seuros/epdiy-esp-idf-6/doc/source/img/board_p2.jpg

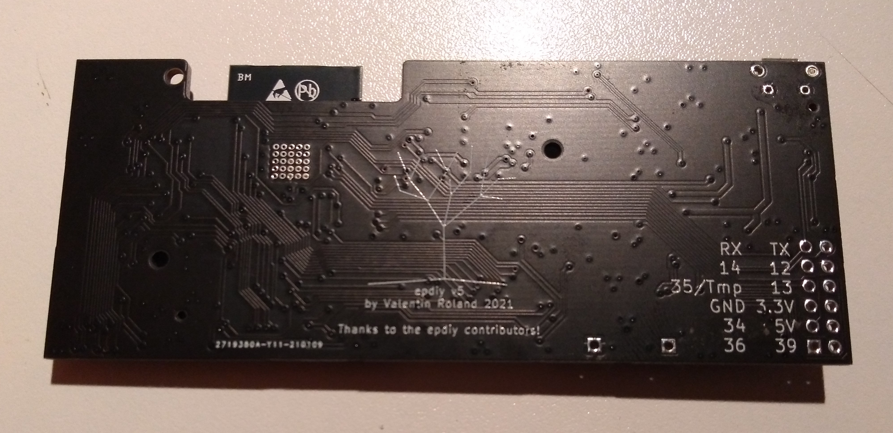
doc/source/img/board_p2.jpg
