seuros/epdiy-esp-idf-6/doc/source/img/ed060sc4.jpg

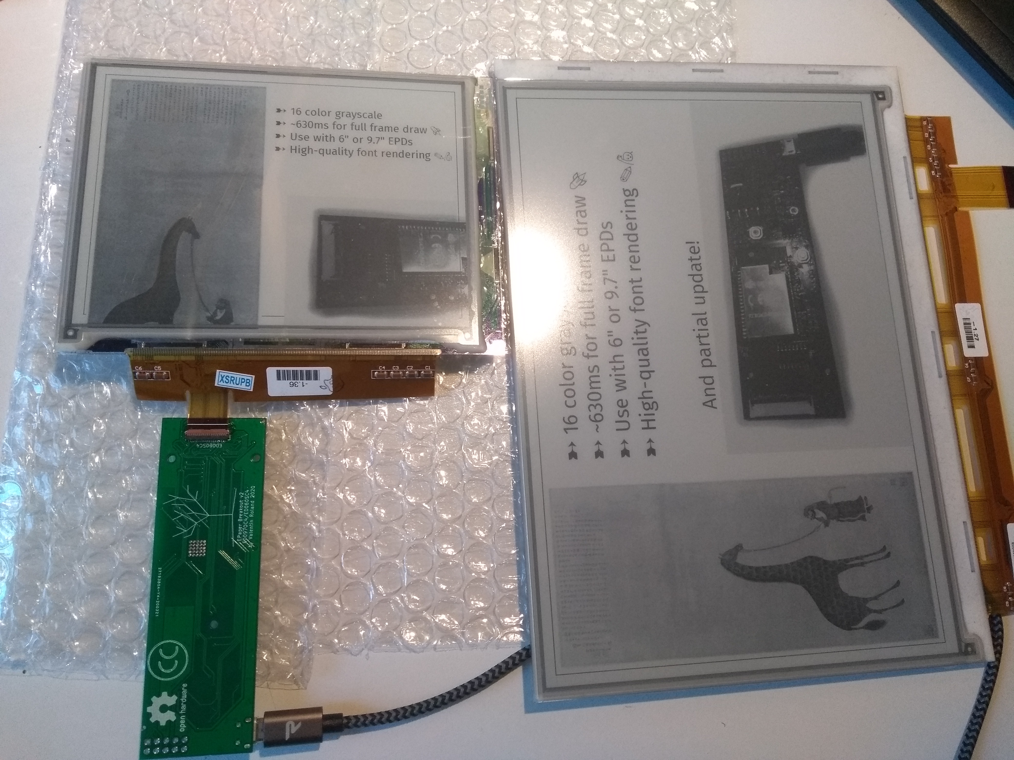
doc/source/img/ed060sc4.jpg
