seuros/epdiy-esp-idf-6/examples/demo/files/beach.jpg

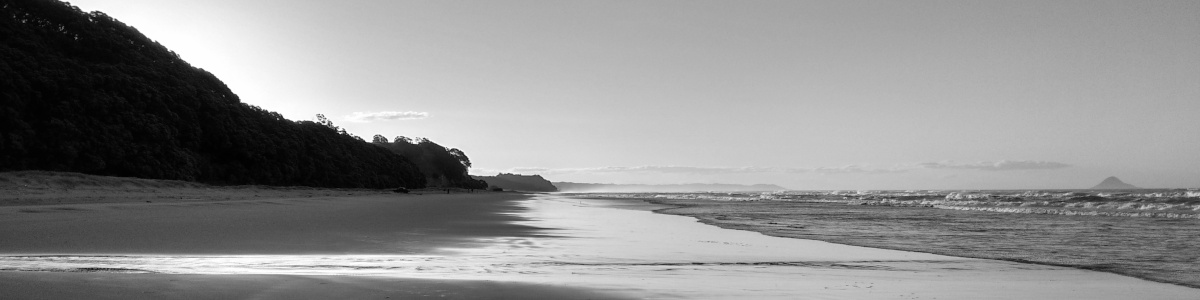
examples/demo/files/beach.jpg
