seuros/epdiy-esp-idf-6/examples/demo/files/board.jpg

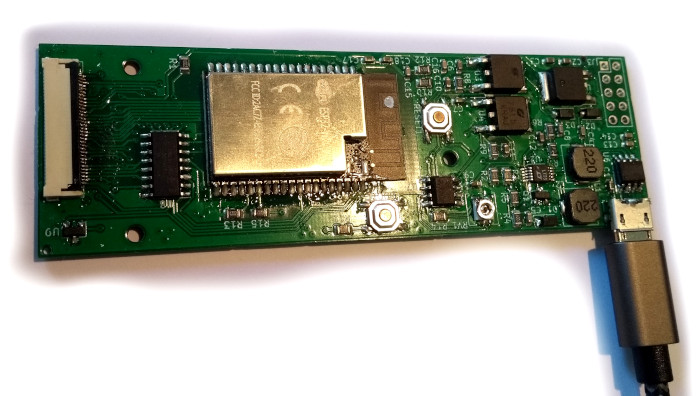
examples/demo/files/board.jpg
