seuros/epdiy-esp-idf-6/examples/demo/files/giraffe.jpg

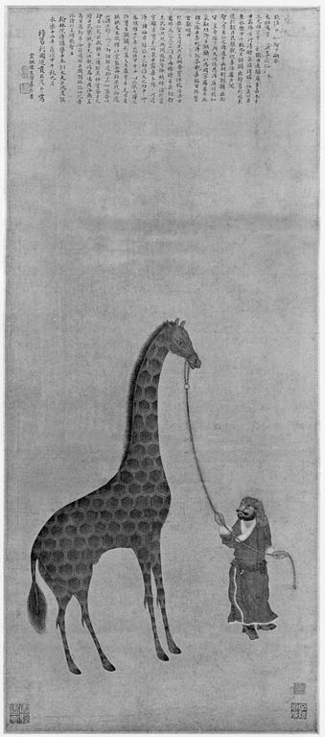
examples/demo/files/giraffe.jpg
