seuros/epdiy-esp-idf-6/examples/demo/files/zebra.jpg

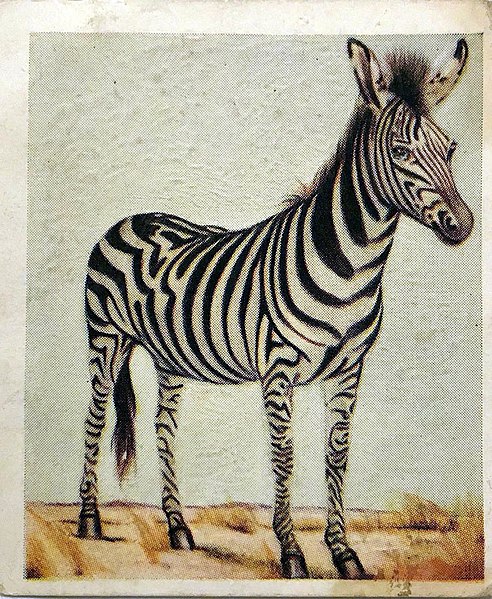
examples/demo/files/zebra.jpg
