seuros/epdiy-esp-idf-6/examples/dragon/cc_dragon.jpg

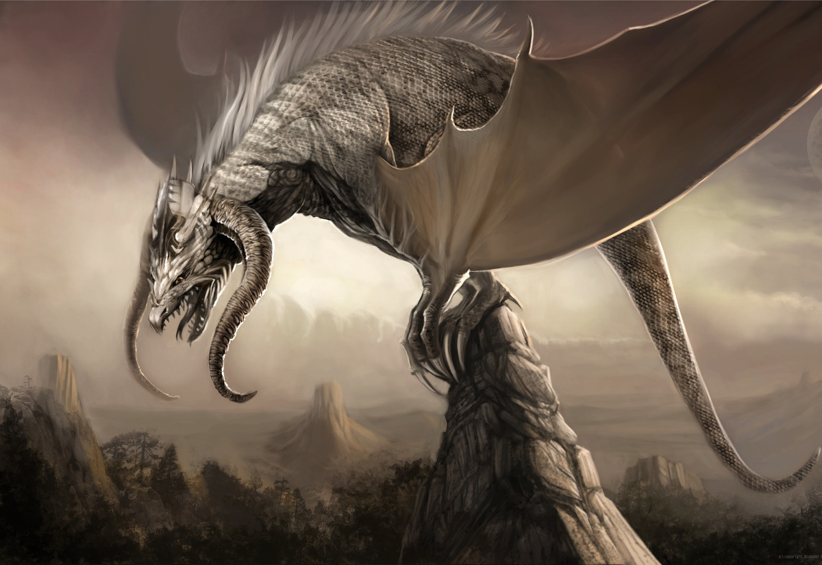
examples/dragon/cc_dragon.jpg
