seuros/epdiy-esp-idf-6/examples/mpd_status/default_album.png

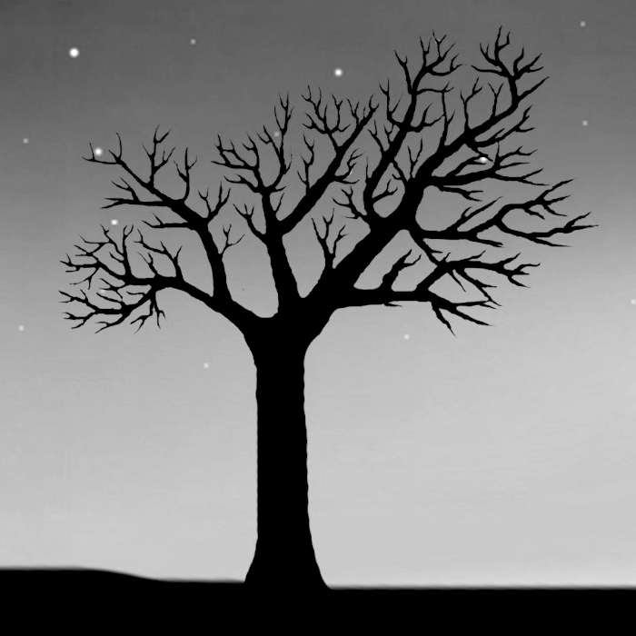
examples/mpd_status/default_album.png
