seuros/epdiy-esp-idf-6/examples/v7-usb-device/data/martin.jpg

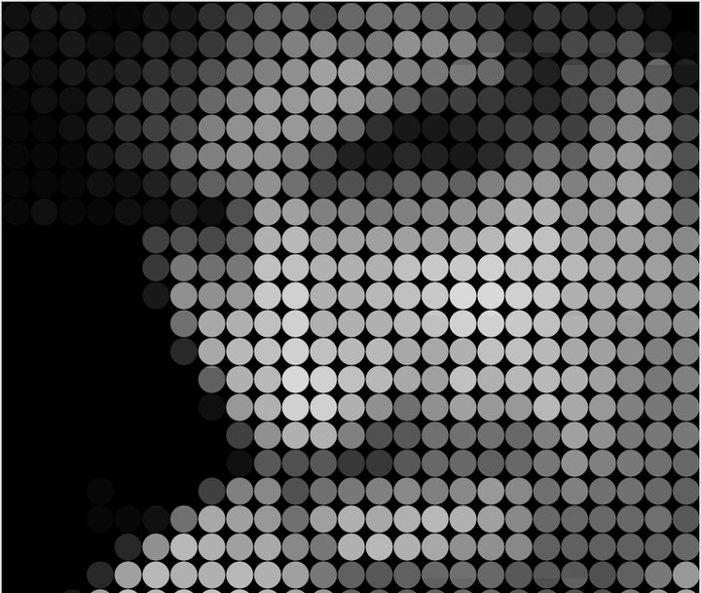
examples/v7-usb-device/data/martin.jpg
