seuros/epdiy-esp-idf-6/examples/weather/weather.jpg

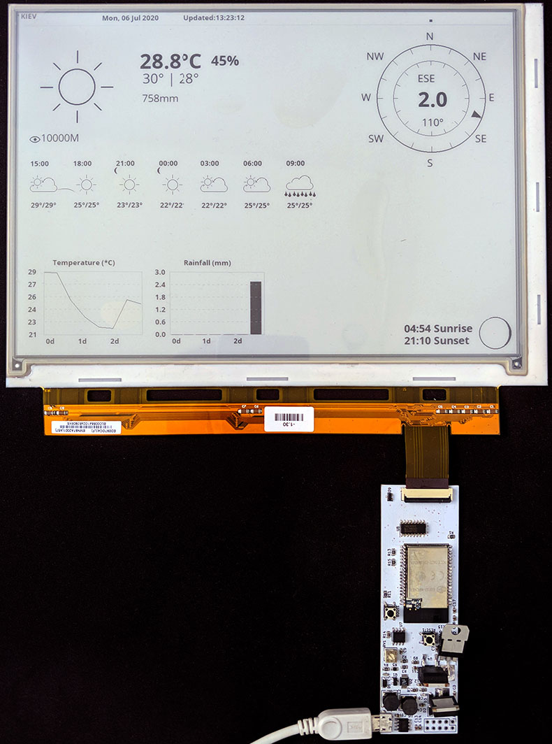
examples/weather/weather.jpg
