seuros/epdiy-esp-idf-6/config_reg_v6.h

#pragma once

#include "display_ops.h"
#include "pca9555.h"
#include "tps65185.h"
#include <driver/i2c.h>
#include <driver/gpio.h>
#include <sys/time.h>

#define CFG_PIN_OE          (PCA_PIN_PC10 >> 8)
#define CFG_PIN_MODE        (PCA_PIN_PC11 >> 8)
#define CFG_PIN_STV         (PCA_PIN_PC12 >> 8)
#define CFG_PIN_PWRUP       (PCA_PIN_PC13 >> 8)
#define CFG_PIN_VCOM_CTRL   (PCA_PIN_PC14 >> 8)
#define CFG_PIN_WAKEUP      (PCA_PIN_PC15 >> 8)
#define CFG_PIN_PWRGOOD     (PCA_PIN_PC16 >> 8)
#define CFG_PIN_INT         (PCA_PIN_PC17 >> 8)

typedef struct {
    i2c_port_t port;
    bool ep_output_enable;
    bool ep_mode;
    bool ep_stv;
    bool pwrup;
    bool vcom_ctrl;
    bool wakeup;
    bool others[8];
} epd_config_register_t;

static bool interrupt_done = false;

static void IRAM_ATTR interrupt_handler(void* arg) {
    interrupt_done = true;
}

int v6_wait_for_interrupt(int timeout) {

    int tries = 0;
    while (!interrupt_done && gpio_get_level(CFG_INTR) == 1) {
        if (tries >= 500) {
            return -1;
        }
        tries++;
        vTaskDelay(1);
    }
    int ival = 0;
    interrupt_done = false;
    pca9555_read_input(EPDIY_I2C_PORT, 1);
	ival = tps_read_register(EPDIY_I2C_PORT, TPS_REG_INT1);
	ival |= tps_read_register(EPDIY_I2C_PORT, TPS_REG_INT2) << 8;
    while (!gpio_get_level(CFG_INTR)) {vTaskDelay(1); }
    return ival;
}

void config_reg_init(epd_config_register_t* reg) {
    reg->ep_output_enable = false;
    reg->ep_mode = false;
    reg->ep_stv = false;
    reg->pwrup = false;
    reg->vcom_ctrl = false;
    reg->wakeup = false;
    for (int i=0; i<8; i++) {
        reg->others[i] = false;
    }

    gpio_set_direction(CFG_INTR, GPIO_MODE_INPUT);
    gpio_set_intr_type(CFG_INTR, GPIO_INTR_NEGEDGE);

    ESP_ERROR_CHECK(gpio_install_isr_service(ESP_INTR_FLAG_EDGE));

    ESP_ERROR_CHECK(gpio_isr_handler_add(CFG_INTR, interrupt_handler, (void *) CFG_INTR));

    // set all epdiy lines to output except TPS interrupt + PWR good
    ESP_ERROR_CHECK(pca9555_set_config(reg->port, CFG_PIN_PWRGOOD | CFG_PIN_INT, 1));
}

static void push_cfg(epd_config_register_t* reg) {
    uint8_t value = 0x00;
    if (reg->ep_output_enable) value |= CFG_PIN_OE;
    if (reg->ep_mode) value |= CFG_PIN_MODE;
    if (reg->ep_stv) value |= CFG_PIN_STV;
    if (reg->pwrup) value |= CFG_PIN_PWRUP;
    if (reg->vcom_ctrl) value |= CFG_PIN_VCOM_CTRL;
    if (reg->wakeup) value |= CFG_PIN_WAKEUP;

    ESP_ERROR_CHECK(pca9555_set_value(reg->port, value, 1));
}

static void cfg_poweron(epd_config_register_t* reg) {
    reg->ep_stv = true;
    reg->wakeup = true;
    push_cfg(reg);
    reg->pwrup = true;
    push_cfg(reg);
    reg->vcom_ctrl = true;
    push_cfg(reg);

    // give the IC time to powerup and set lines
    vTaskDelay(1);

    while (!(pca9555_read_input(reg->port, 1) & CFG_PIN_PWRGOOD)) {
        vTaskDelay(1);
    }

    ESP_ERROR_CHECK(tps_write_register(reg->port, TPS_REG_ENABLE, 0x3F));

#ifdef CONFIG_EPD_DRIVER_V6_VCOM
    tps_set_vcom(reg->port, CONFIG_EPD_DRIVER_V6_VCOM);
// Arduino IDE...
#else
    extern int epd_driver_v6_vcom;
    tps_set_vcom(reg->port, epd_driver_v6_vcom);
#endif

    gpio_set_level(STH, 1);

    int tries = 0;
    while (!((tps_read_register(reg->port, TPS_REG_PG) & 0xFA) == 0xFA)) {
        if (tries >= 500) {
            ESP_LOGE("epdiy", "Power enable failed! PG status: %X", tps_read_register(reg->port, TPS_REG_PG));
            return;
        }
        tries++;
        vTaskDelay(1);
    }
}

static void cfg_poweroff(epd_config_register_t* reg) {
    reg->vcom_ctrl = false;
    reg->pwrup = false;
    reg->ep_stv = false;
    reg->ep_output_enable = false;
    reg->ep_mode = false;
    push_cfg(reg);
    vTaskDelay(1);
    reg->wakeup = false;
    push_cfg(reg);
}

static void cfg_deinit(epd_config_register_t* reg) {
    ESP_ERROR_CHECK(pca9555_set_config(reg->port, CFG_PIN_PWRGOOD | CFG_PIN_INT | CFG_PIN_VCOM_CTRL | CFG_PIN_PWRUP, 1));

    int tries = 0;
    while (!((pca9555_read_input(reg->port, 1) & 0xC0) == 0x80)) {
        if (tries >= 500) {
            ESP_LOGE("epdiy", "failed to shut down TPS65185!");
            break;
        }
        tries++;
        vTaskDelay(1);
        printf("%X\n", pca9555_read_input(reg->port, 1));
    }
    // Not sure why we need this delay, but the TPS65185 seems to generate an interrupt after some time that needs to be cleared.
    vTaskDelay(500);
    pca9555_read_input(reg->port, 0);
    pca9555_read_input(reg->port, 1);
    ESP_LOGI("epdiy", "going to sleep.");
}
