seuros/epdiy-esp-idf-6/display_ops.h

#pragma once

#include "driver/gpio.h"

#if defined(CONFIG_EPD_BOARD_REVISION_V5) || defined(CONFIG_EPD_BOARD_REVISION_V6)
#define D7 GPIO_NUM_23
#define D6 GPIO_NUM_22
#define D5 GPIO_NUM_21
#define D4 GPIO_NUM_19
#define D3 GPIO_NUM_18
#define D2 GPIO_NUM_5
#define D1 GPIO_NUM_4
#define D0 GPIO_NUM_25

/* Control Lines */
#define CKV GPIO_NUM_26
#define STH GPIO_NUM_27

#define V4_LATCH_ENABLE GPIO_NUM_2

/* Edges */
#define CKH GPIO_NUM_15

#if defined(CONFIG_EPD_BOARD_REVISION_V5)
/* Config Reggister Control */
#define CFG_DATA GPIO_NUM_33
#define CFG_CLK GPIO_NUM_32
#define CFG_STR GPIO_NUM_0
#endif
#if defined(CONFIG_EPD_BOARD_REVISION_V6)
#define CFG_SCL GPIO_NUM_33
#define CFG_SDA GPIO_NUM_32
#define CFG_INTR GPIO_NUM_35

#define EPDIY_I2C_PORT I2C_NUM_0
#endif

#else
#define D7 GPIO_NUM_22
#define D6 GPIO_NUM_21
#define D5 GPIO_NUM_27
#define D4 GPIO_NUM_2
#if defined(CONFIG_EPD_BOARD_REVISION_LILYGO_T5_47)
#define D3 GPIO_NUM_19
#else
#define D3 GPIO_NUM_0
#endif
#define D2 GPIO_NUM_4
#define D1 GPIO_NUM_32
#define D0 GPIO_NUM_33

#define CFG_DATA GPIO_NUM_23
#define CFG_CLK GPIO_NUM_18
#if defined(CONFIG_EPD_BOARD_REVISION_LILYGO_T5_47)
#define CFG_STR GPIO_NUM_0
#else
#define CFG_STR GPIO_NUM_19
#endif

/* Control Lines */
#define CKV GPIO_NUM_25
#define STH GPIO_NUM_26

#define V4_LATCH_ENABLE GPIO_NUM_15

/* Edges */
#define CKH GPIO_NUM_5

#endif

void epd_base_init(uint32_t epd_row_width);
void epd_base_deinit();
void epd_poweron();
void epd_poweroff();

/**
 * Start a draw cycle.
 */
void epd_start_frame();

/**
 * End a draw cycle.
 */
void epd_end_frame();

/**
 * Waits until all previously submitted data has been written.
 * Then, the following operations are initiated:
 *
 *  - Previously submitted data is latched to the output register.
 *  - The RMT peripheral is set up to pulse the vertical (gate) driver for
 *  `output_time_dus` / 10 microseconds.
 *  - The I2S peripheral starts transmission of the current buffer to
 *  the source driver.
 *  - The line buffers are switched.
 *
 * This sequence of operations allows for pipelining data preparation and
 * transfer, reducing total refresh times.
 */
void IRAM_ATTR epd_output_row(uint32_t output_time_dus);

/** Skip a row without writing to it. */
void IRAM_ATTR epd_skip();

/**
 * Get the currently writable line buffer.
 */
uint8_t IRAM_ATTR *epd_get_current_buffer();

/**
 * Switches front and back line buffer.
 * If the switched-to line buffer is currently in use,
 * this function blocks until transmission is done.
 */
void IRAM_ATTR epd_switch_buffer();
