seuros/epdiy-esp-idf-6/src/builtin_waveforms.c

#include "epdiy.h"

#include "waveforms/epdiy_ED047TC1.h"

// Note: Alternative Waveform added by Lilygo on Oct 2021, size: 266 Kb (ED047TC1 is 37 Kb, 7 times
// smaller)
#include "waveforms/epdiy_ED047TC2.h"

#include "waveforms/epdiy_ED060SC4.h"
#include "waveforms/epdiy_ED060SCT.h"
#include "waveforms/epdiy_ED060XC3.h"
#include "waveforms/epdiy_ED097OC4.h"
#include "waveforms/epdiy_ED097TC2.h"
#include "waveforms/epdiy_ED133UT2.h"
#include "waveforms/epdiy_NULL.h"
