seuros/epdiy-esp-idf-6/src/epd_driver/rmt_pulse.h

/**
 * Emit a pulse of precise length on a pin, using the RMT peripheral.
 */

#pragma once
#include "driver/gpio.h"
#include "esp_attr.h"
#include <stdint.h>

/**
 * Initializes RMT Channel 0 with a pin for RMT pulsing.
 * The pin will have to be re-initialized if subsequently used as GPIO.
 */
void rmt_pulse_init(gpio_num_t pin);

/**
 * Outputs a single pulse (high -> low) on the configured pin.
 * This function will always wait for a previous call to finish.
 *
 * @param: high_time_us Pulse high time in us.
 * @param: low_time_us Pulse low time in us.
 * @param: wait Block until the pulse is finished.
 */
void pulse_ckv_us(uint16_t high_time_us, uint16_t low_time_us,
                  bool wait);
/**
 * Indicates if the rmt is currently sending a pulse.
 */
bool rmt_busy();

/**
 * Outputs a single pulse (high -> low) on the configured pin.
 * This function will always wait for a previous call to finish.
 *
 * @param: high_time_us Pulse high time clock ticks.
 * @param: low_time_us Pulse low time in clock ticks.
 * @param: wait Block until the pulse is finished.
 */
void pulse_ckv_ticks(uint16_t high_time_us, uint16_t low_time_us,
                     bool wait);
