seuros/epdiy-esp-idf-6/builtin_waveforms.c

#include "epd_driver.h"


#include "waveforms/epdiy_ED047TC1.h"
#include "waveforms/epdiy_ED047TC2.h"
#include "waveforms/epdiy_ED060SC4.h"
#include "waveforms/epdiy_ED060XC3.h"
#include "waveforms/epdiy_ED060SCT.h"
#include "waveforms/epdiy_ED097OC4.h"
#include "waveforms/epdiy_ED097TC2.h"
#include "waveforms/epdiy_ED133UT2.h"
