seuros/epdiy-esp-idf-6/examples/weather/main/opensans6.h

#pragma once
#include "epd_driver.h"
const uint8_t OpenSansBitmaps[50198] = {
    0x78, 0x9C, 0x03, 0x00, 0x00, 0x00, 0x00, 0x01, 0x78, 0x9C, 0x7B, 0xC0, 0x7A, 0x81, 0xE5, 0x00,
    0xCB, 0x06, 0xE6, 0x05, 0x4C, 0x13, 0x18, 0x19, 0x18, 0x26, 0x30, 0x5F, 0x60, 0x05, 0x00, 0x3F,
    0x3F, 0x05, 0xCC, 0x78, 0x9C, 0xFB, 0x78, 0x80, 0xF5, 0xC1, 0x02, 0xE6, 0x03, 0x13, 0x98, 0x00,
    0x1A, 0x73, 0x04, 0x8C, 0x78, 0x9C, 0x63, 0xB8, 0x20, 0xC0, 0xC3, 0xC0, 0xB0, 0x29, 0x80, 0x83,
    0xE1, 0xD2, 0xBB, 0xB7, 0x77, 0x19, 0x18, 0x3C, 0x0E, 0x30, 0x32, 0x30, 0xC8, 0x5C, 0x60, 0x60,
    0xB8, 0x71, 0xFF, 0x6D, 0x2D, 0x83, 0x02, 0x77, 0x2B, 0x03, 0x83, 0x03, 0x67, 0x04, 0x03, 0x43,
    0x01, 0x9B, 0x15, 0x03, 0x03, 0x00, 0x46, 0x02, 0x0C, 0x98, 0x78, 0x9C, 0x63, 0xD8, 0xC0, 0xC4,
    0x60, 0xF0, 0xE7, 0x1C, 0xD3, 0x83, 0x2D, 0x42, 0x0C, 0x1F, 0x36, 0x32, 0x31, 0x2C, 0x38, 0xC3,
    0xC4, 0xC0, 0xF0, 0x2C, 0x96, 0x81, 0x61, 0xC3, 0x53, 0x16, 0x86, 0x0D, 0x4D, 0x1C, 0x86, 0x1B,
    0x0E, 0xB3, 0x1E, 0xFC, 0x97, 0x0B, 0xE4, 0x33, 0x31, 0x00, 0x00, 0x6F, 0x71, 0x10, 0x03, 0x78,
    0x9C, 0x9B, 0x30, 0x87, 0xE1, 0x00, 0x13, 0xC3, 0xA6, 0x05, 0xCC, 0x6D, 0x0C, 0x0C, 0x2D, 0x05,
    0x6C, 0xBC, 0x20, 0xB2, 0xED, 0x84, 0x0F, 0x50, 0xE4, 0x68, 0xC4, 0x41, 0x86, 0x86, 0x35, 0xD6,
    0xDA, 0x17, 0x18, 0x18, 0x1C, 0xB8, 0x40, 0xE4, 0x01, 0x26, 0xA0, 0x08, 0x43, 0x1B, 0xC3, 0x41,
    0x1F, 0x06, 0x00, 0xF5, 0x4D, 0x11, 0xA4, 0x78, 0x9C, 0x63, 0x78, 0x99, 0xC7, 0xC0, 0xE0, 0xC0,
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
    { 4, 9, 4, 0, 6, 25, 7993 }, // ⁏
    { 7, 7, 9, 1, 8, 27, 8018 }, // ⁐
    { 6, 11, 6, 0, 9, 38, 8045 }, // ⁑
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
};
const EpdUnicodeInterval OpenSansIntervals[] = {
    { 0x20, 0x7E, 0x0 },
    { 0xA0, 0xFF, 0x5F },
    { 0x2010, 0x205F, 0xBF },
    { 0x2190, 0x21FF, 0x10F },
    { 0x2300, 0x23FF, 0x17F },
    { 0x25A0, 0x25FF, 0x27F },
    { 0x2600, 0x26F0, 0x2DF },
    { 0x2700, 0x27BF, 0x3D0 },
};
const EpdFont OpenSans = {
    OpenSansBitmaps,
    OpenSansGlyphs,
    OpenSansIntervals,
    8,
    1,
    17,
    14,
    -4,
};
